Jeremy924/GameController/GameController/GameController.kicad_sch

## KiCad design GameController/GameController.kicad_sch (2024-01-13)

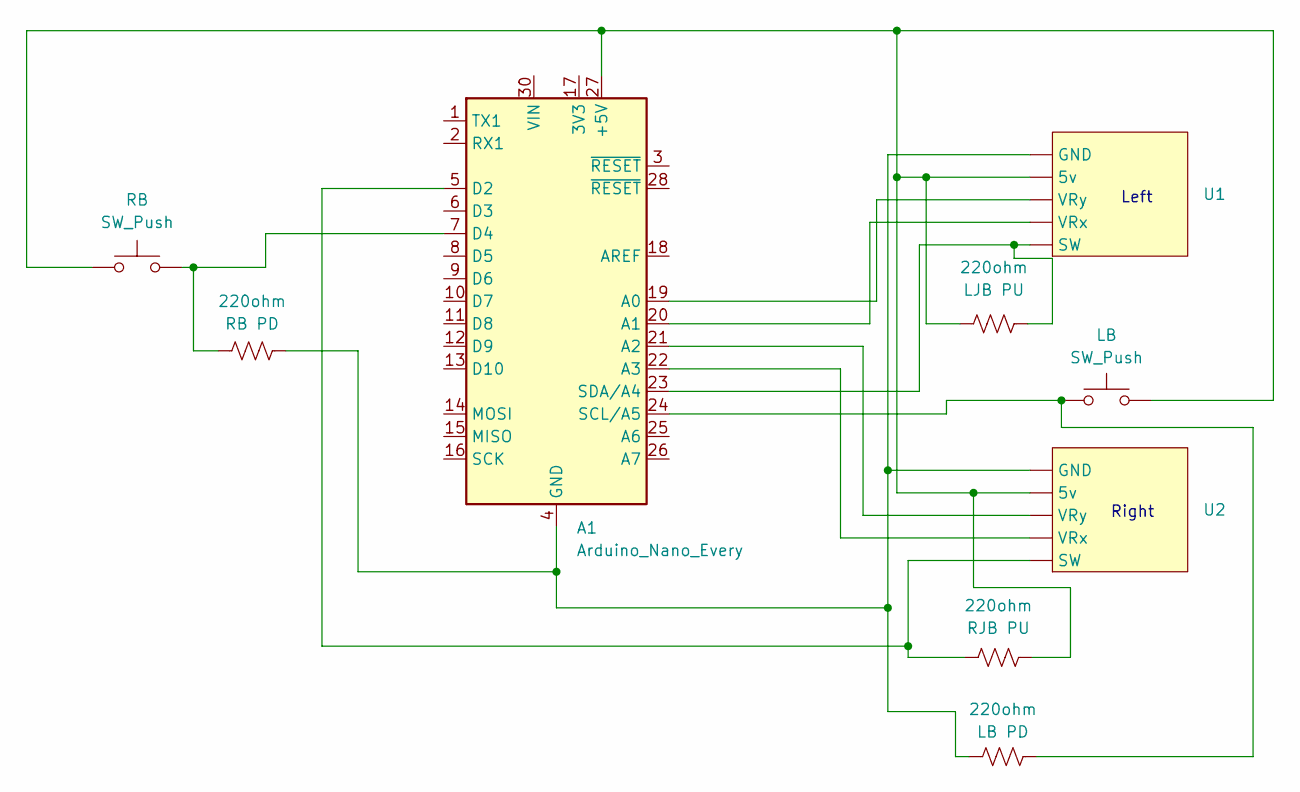
[picture p5: schematic GameController.kicad_sch]

Parts:
220ohm: LJB PU
A1: Arduino_Nano_Every; Arduino_Nano
LB: SW_Push
RB: SW_Push
U1, U2: (no value)

Connections:
unnamed: 220ohm.1, 220ohm.2, A1.4 (GND), A1.5 (D2), A1.7 (D4), A1.27 (+5V), A1.29 (GND), LB.2, RB.1, RB.2, U1., U2.
unnamed: 220ohm.2, A1.23 (SDA/A4), A1.24 (SCL/A5), LB.1, U1.
unnamed: A1.19 (A0), U1.
unnamed: A1.20 (A1), U1.
unnamed: A1.21 (A2), U2.
unnamed: A1.22 (A3), U2.

Notes on the sheet:
Left
Right
